wolff-jonas/cj4-cdu/images/button.png

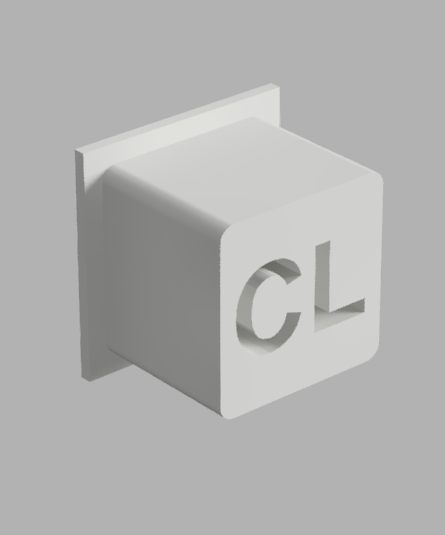
images/button.png
