wolff-jonas/cj4-cdu/images/keyboard.jpg

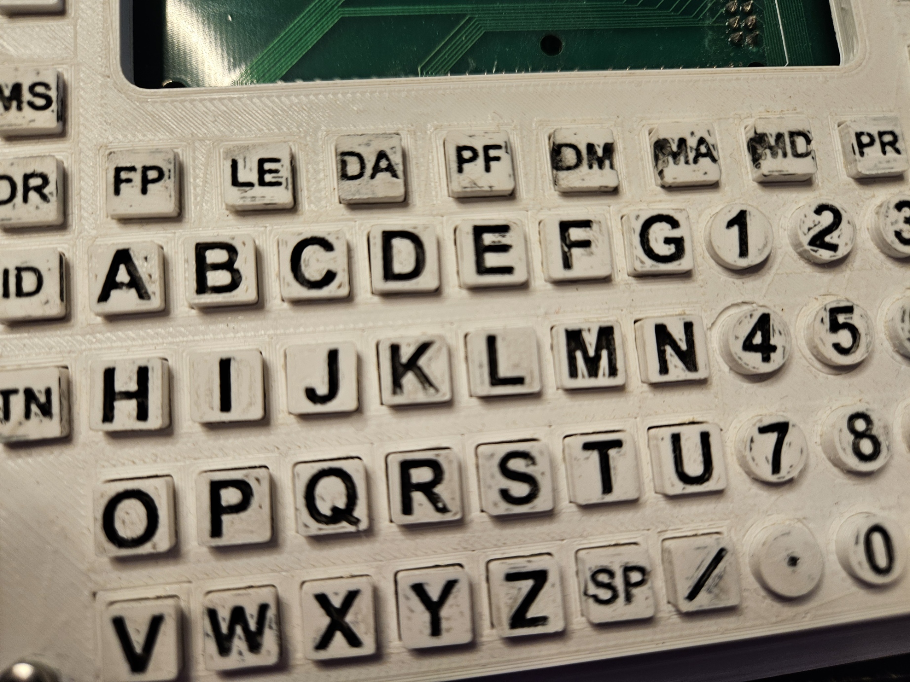
images/keyboard.jpg
